Janky-Jingle-Crew/NorthPoleCircuit/Media/decorations.jpg

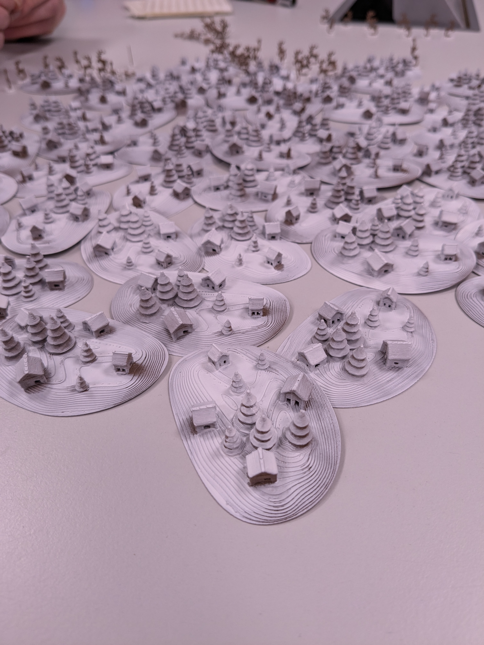
Media/decorations.jpg
