Janky-Jingle-Crew/NorthPoleCircuit/Media/decorations_2.jpg

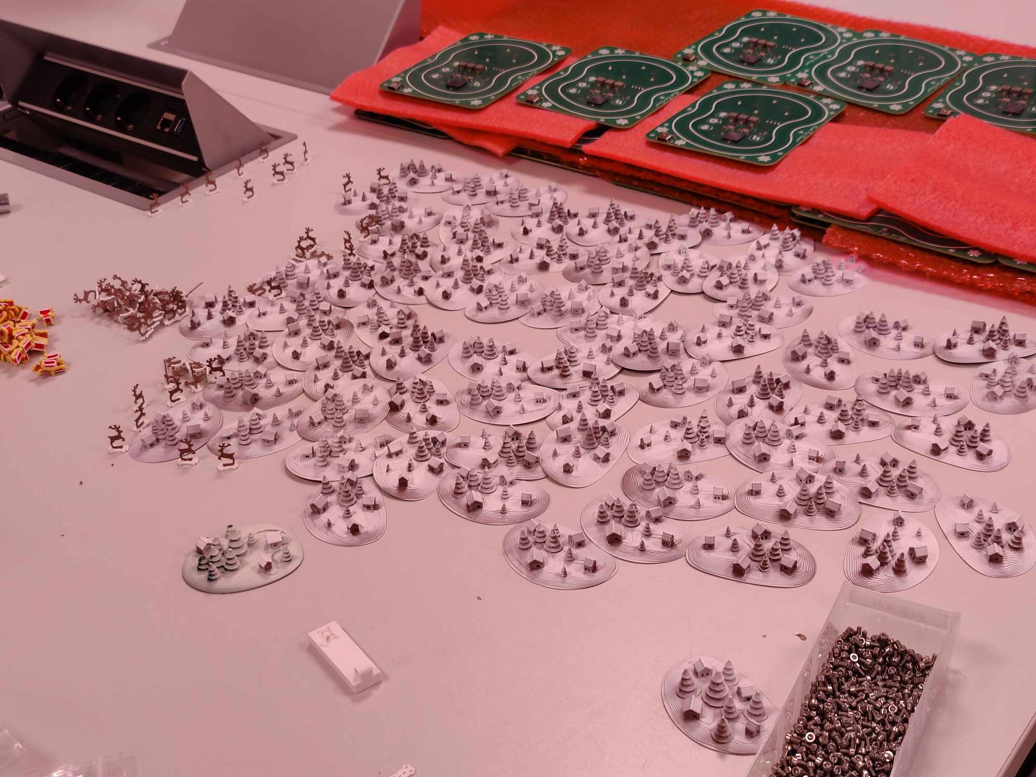
Media/decorations_2.jpg
