Janky-Jingle-Crew/NorthPoleCircuit/Media/decorations_3.jpg

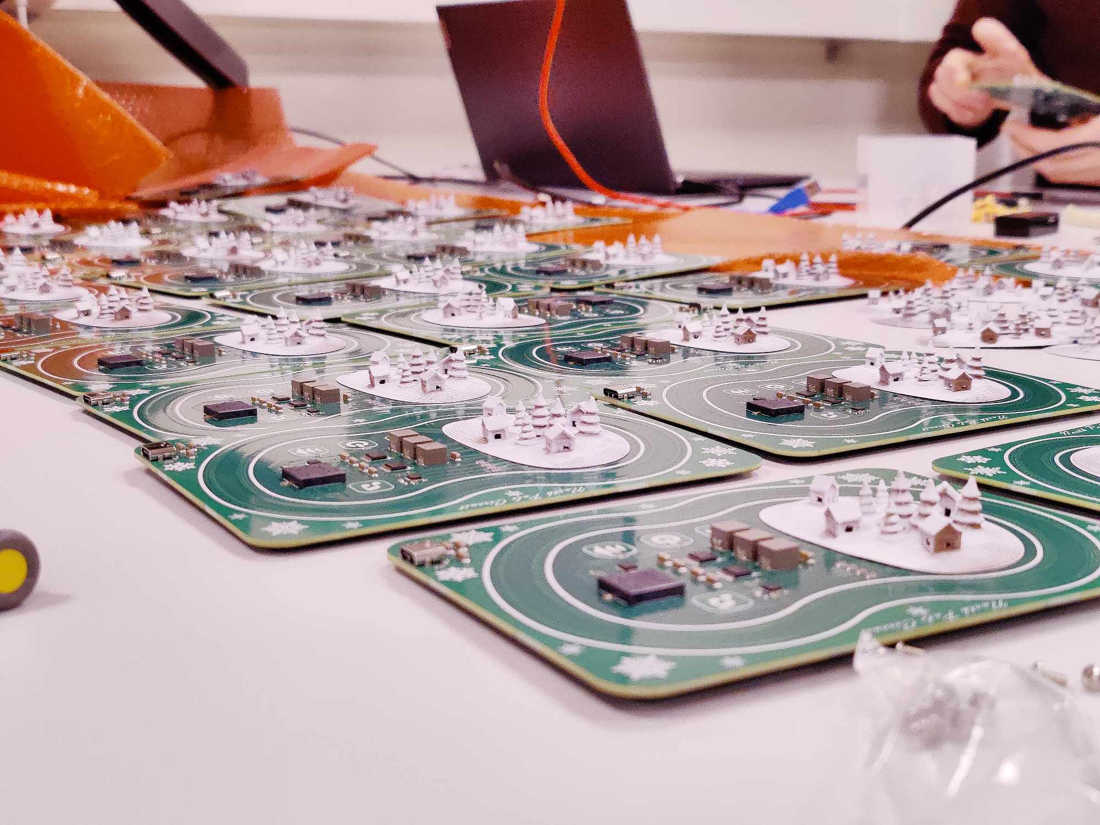
Media/decorations_3.jpg
