Janky-Jingle-Crew/NorthPoleCircuit/Media/pcbs.jpg

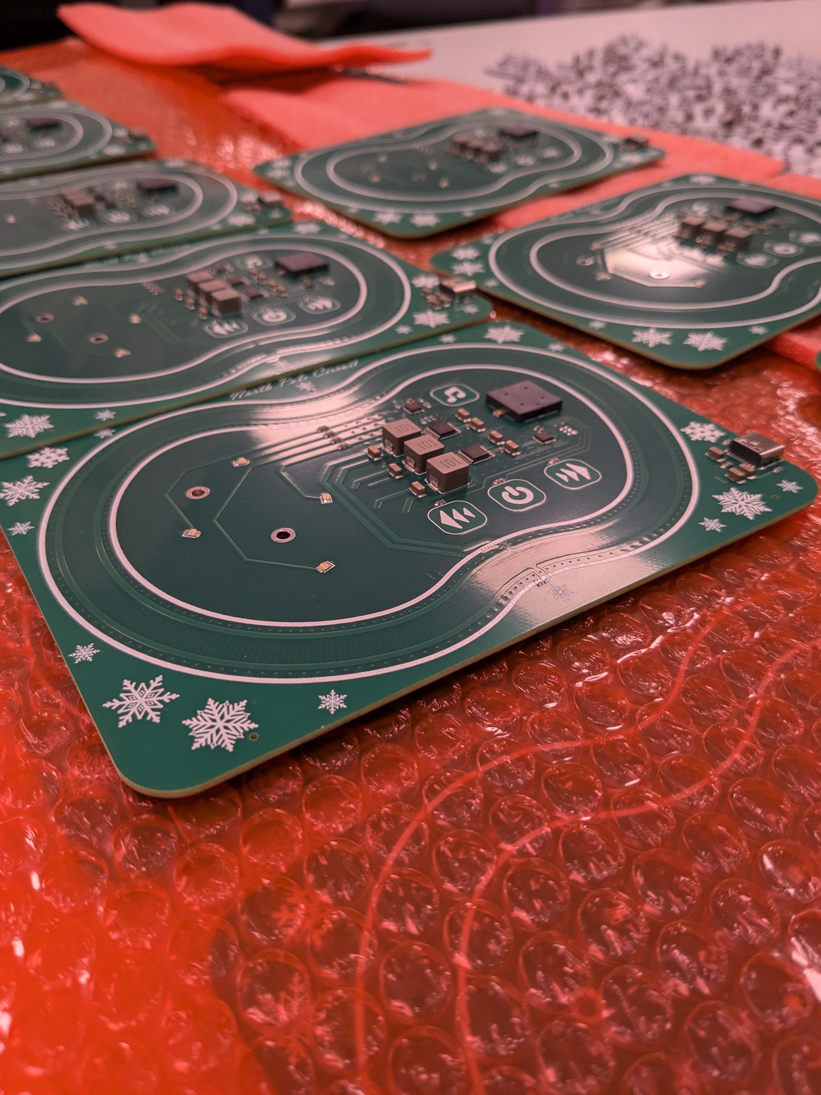
Media/pcbs.jpg
