Janky-Jingle-Crew/NorthPoleCircuit/Media/production_glueing.jpg

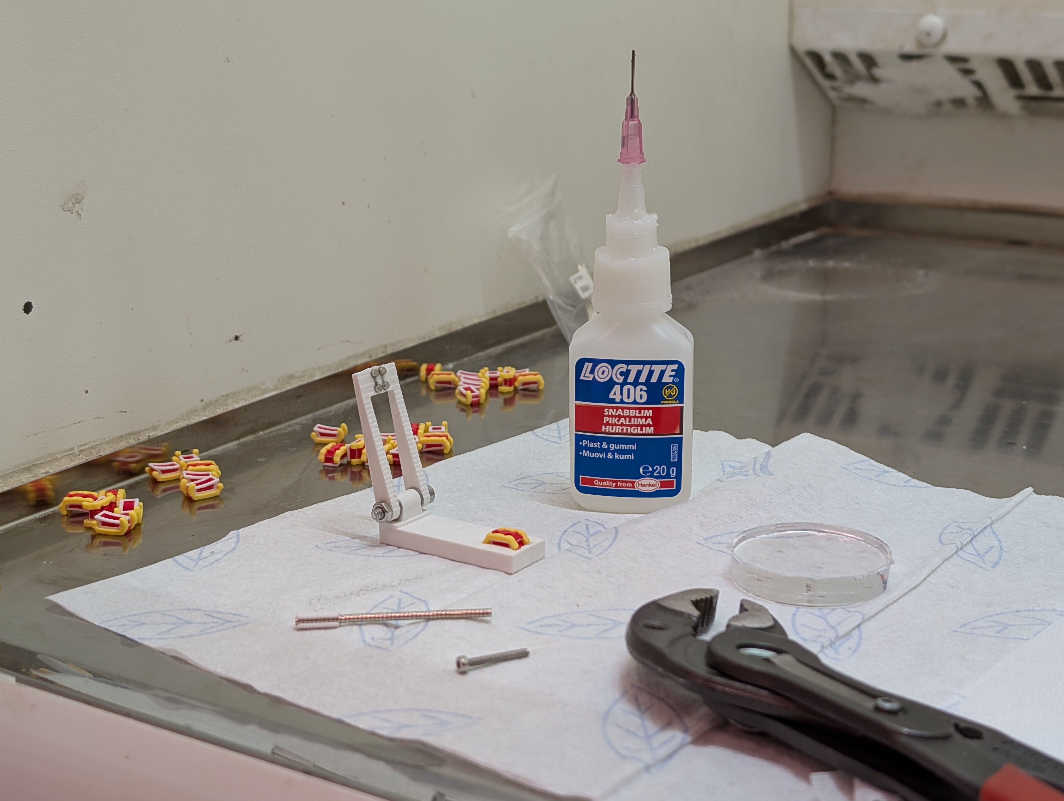
Media/production_glueing.jpg
