Janky-Jingle-Crew/NorthPoleCircuit/Media/single_decoration_2.jpg

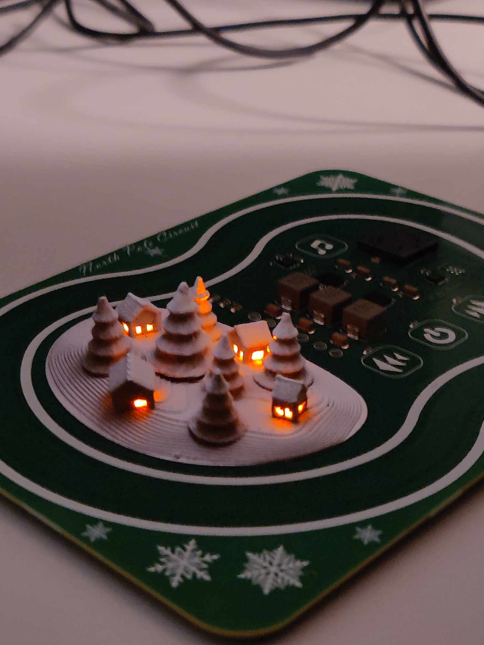
Media/single_decoration_2.jpg
