Janky-Jingle-Crew/NorthPoleCircuit/PCB/Pictures/Edwardian Script ITC 350/text_and_a_happy_new_year.png

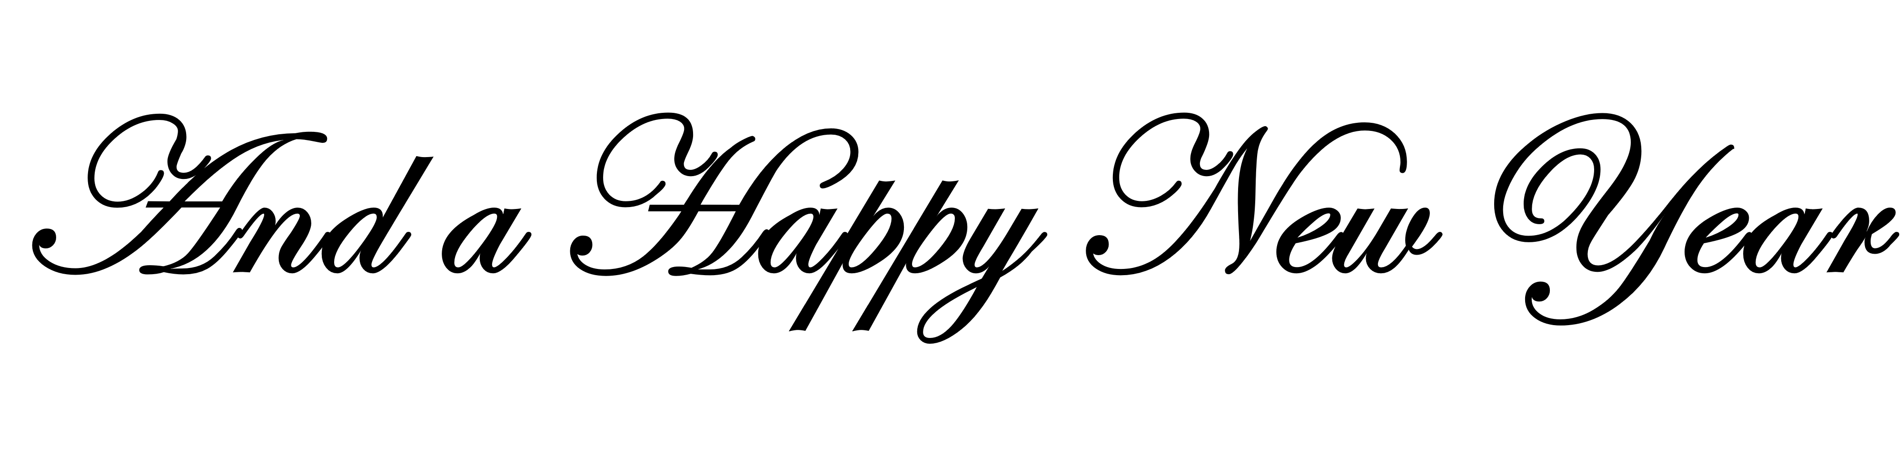
PCB/Pictures/Edwardian Script ITC 350/text_and_a_happy_new_year.png
