Janky-Jingle-Crew/NorthPoleCircuit/PCB/Pictures/Edwardian Script ITC 350/text_DQ.png

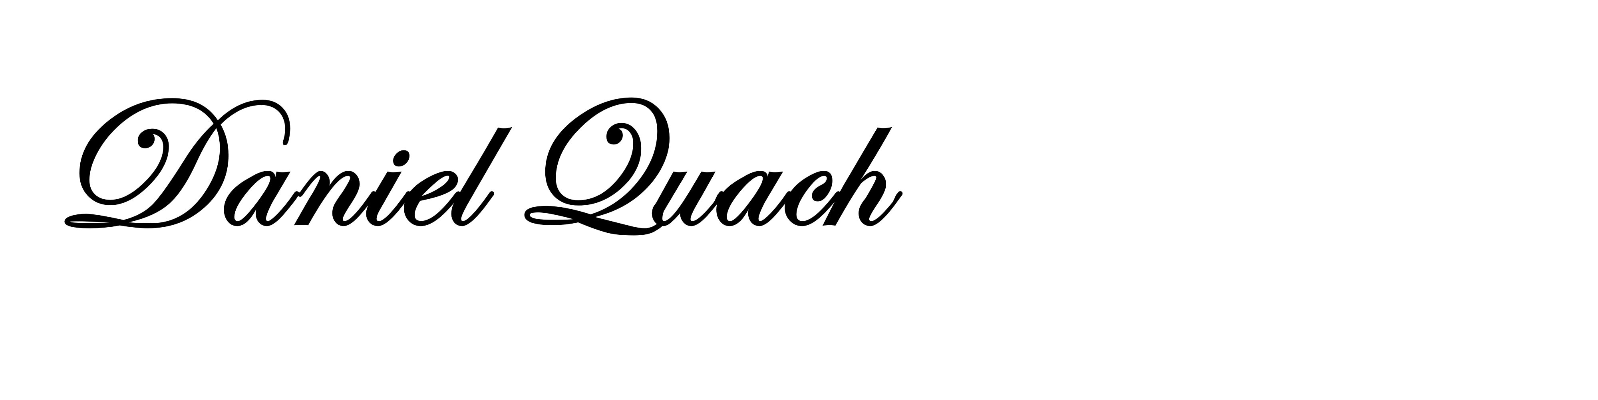
PCB/Pictures/Edwardian Script ITC 350/text_DQ.png
