Janky-Jingle-Crew/NorthPoleCircuit/PCB/Pictures/Edwardian Script ITC 350/text_GA.png

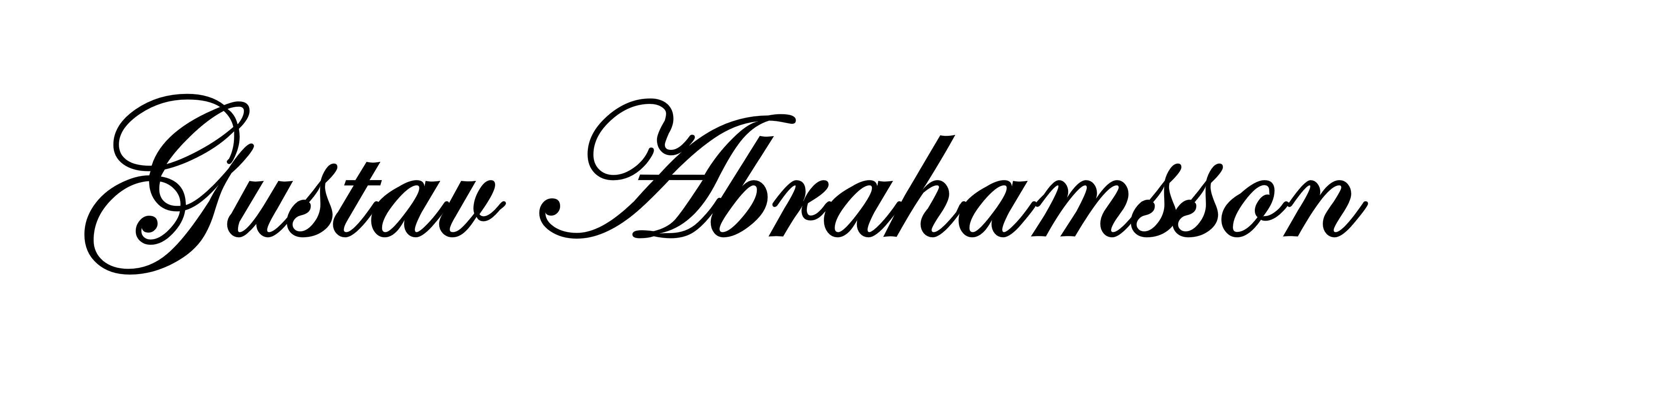
PCB/Pictures/Edwardian Script ITC 350/text_GA.png
