Janky-Jingle-Crew/NorthPoleCircuit/PCB/Pictures/Edwardian Script ITC 350/text_janky_jingle_crew_2024.png

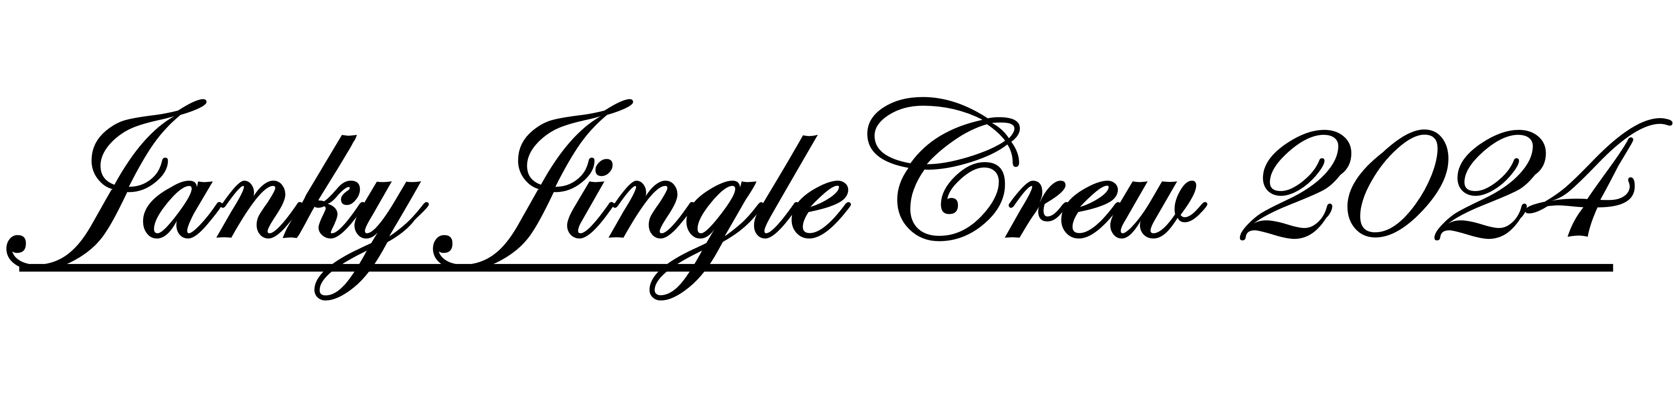
PCB/Pictures/Edwardian Script ITC 350/text_janky_jingle_crew_2024.png
