Janky-Jingle-Crew/NorthPoleCircuit/PCB/Pictures/Edwardian Script ITC 350/text_JW.png

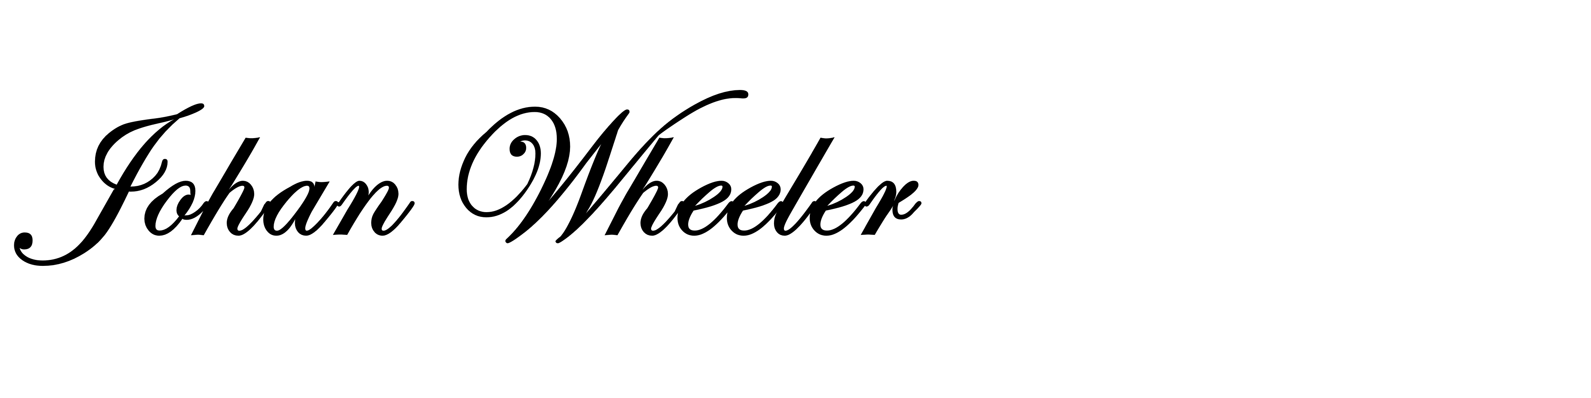
PCB/Pictures/Edwardian Script ITC 350/text_JW.png
