Janky-Jingle-Crew/NorthPoleCircuit/PCB/Pictures/Edwardian Script ITC 350/text_merry_christmas.png

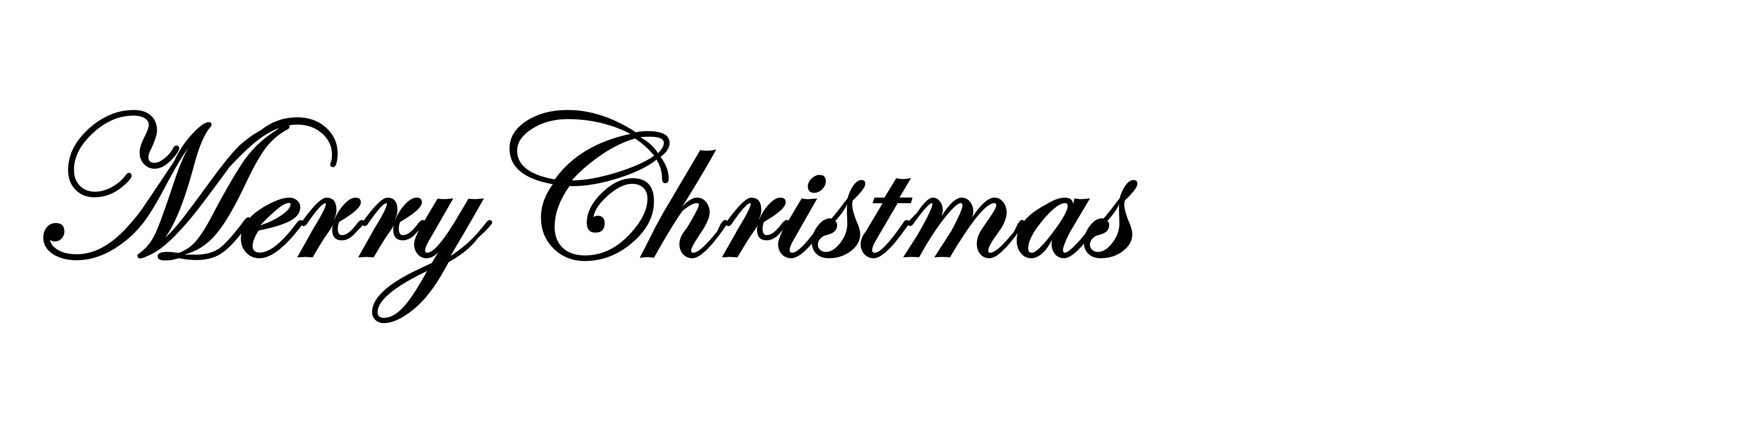
PCB/Pictures/Edwardian Script ITC 350/text_merry_christmas.png
