Janky-Jingle-Crew/NorthPoleCircuit/PCB/Pictures/Edwardian Script ITC 350/text_north_pole_circuit.png

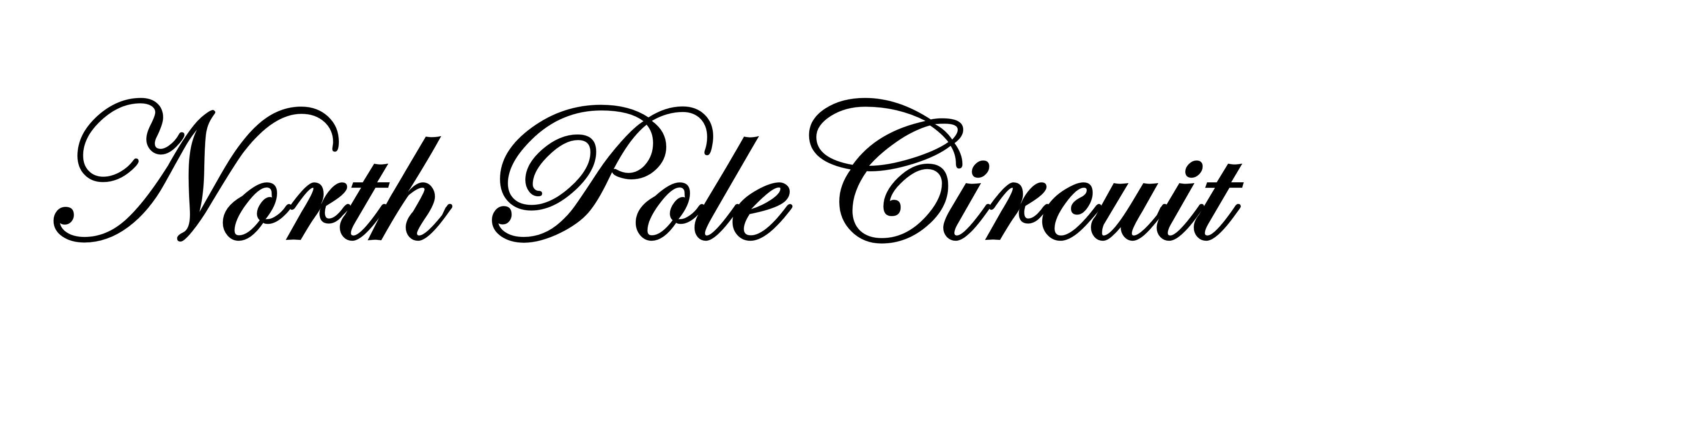
PCB/Pictures/Edwardian Script ITC 350/text_north_pole_circuit.png
