Janky-Jingle-Crew/NorthPoleCircuit/PCB/Pictures/Kunsler Script 350/text_AA.png

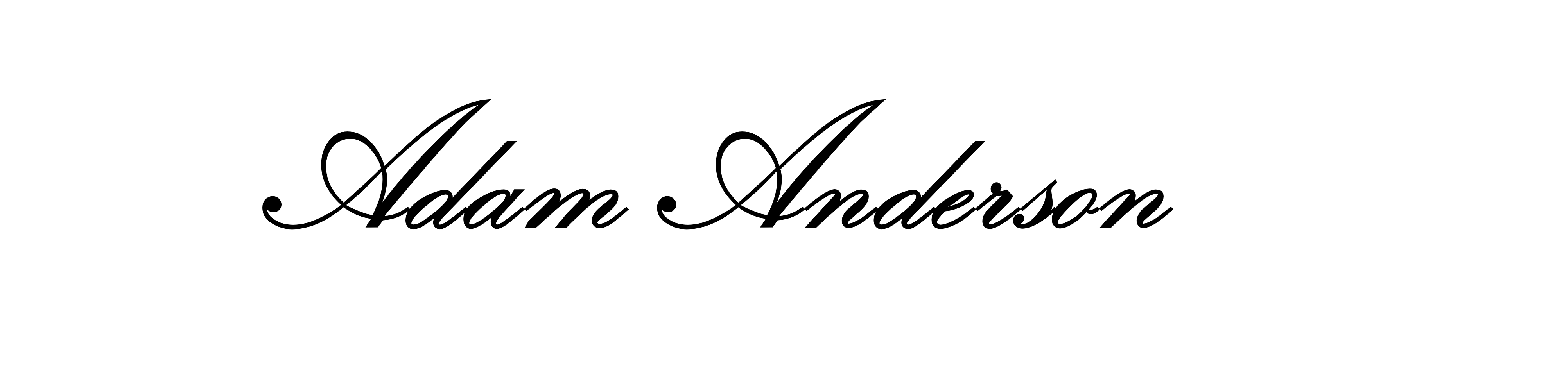
PCB/Pictures/Kunsler Script 350/text_AA.png
