Janky-Jingle-Crew/NorthPoleCircuit/PCB/Pictures/Kunsler Script 350/text_and_a_happy_new_year_small_a.png

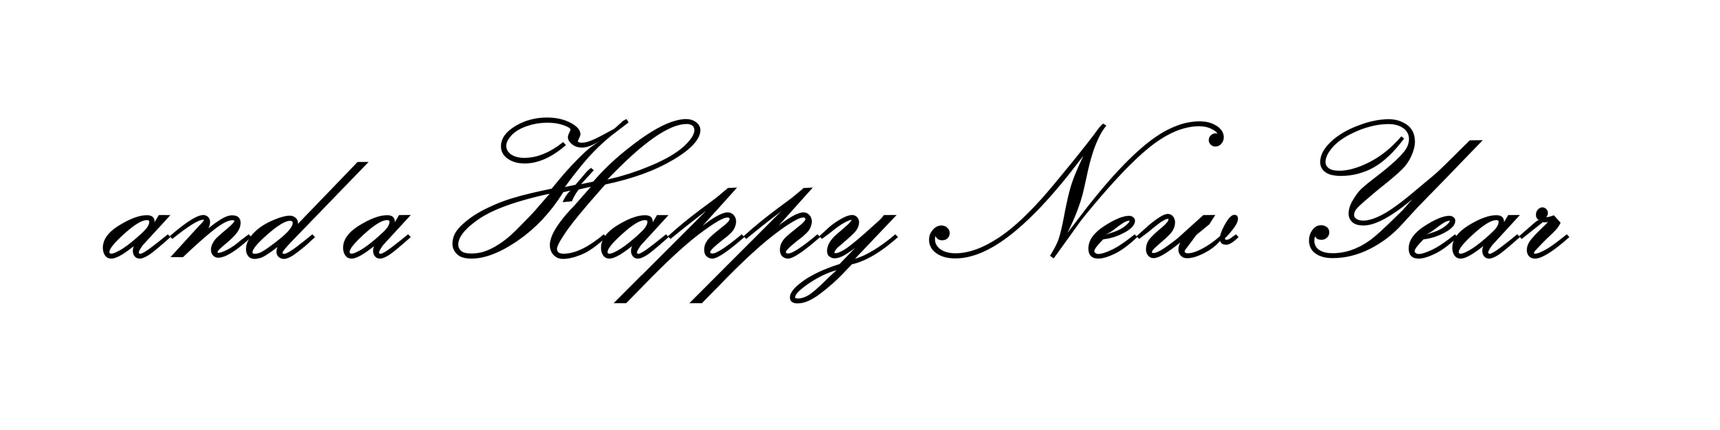
PCB/Pictures/Kunsler Script 350/text_and_a_happy_new_year_small_a.png
