Janky-Jingle-Crew/NorthPoleCircuit/PCB/Pictures/Kunsler Script 350/text_DQ.png

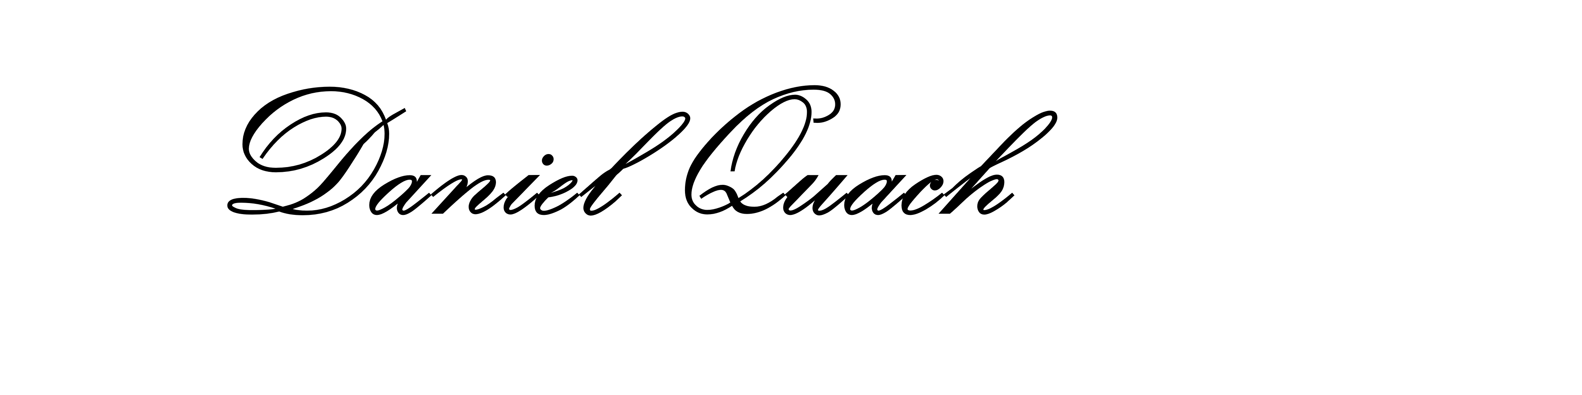
PCB/Pictures/Kunsler Script 350/text_DQ.png
