Janky-Jingle-Crew/NorthPoleCircuit/PCB/Pictures/Kunsler Script 350/text_GA.png

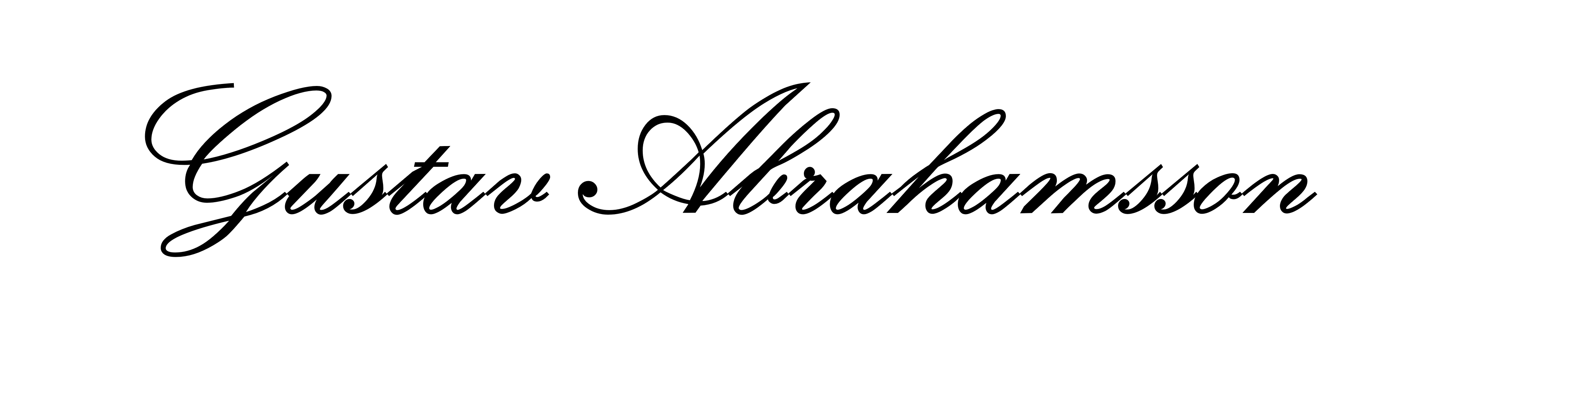
PCB/Pictures/Kunsler Script 350/text_GA.png
