Janky-Jingle-Crew/NorthPoleCircuit/PCB/Pictures/Kunsler Script 350/text_jankyjinglecrew.png

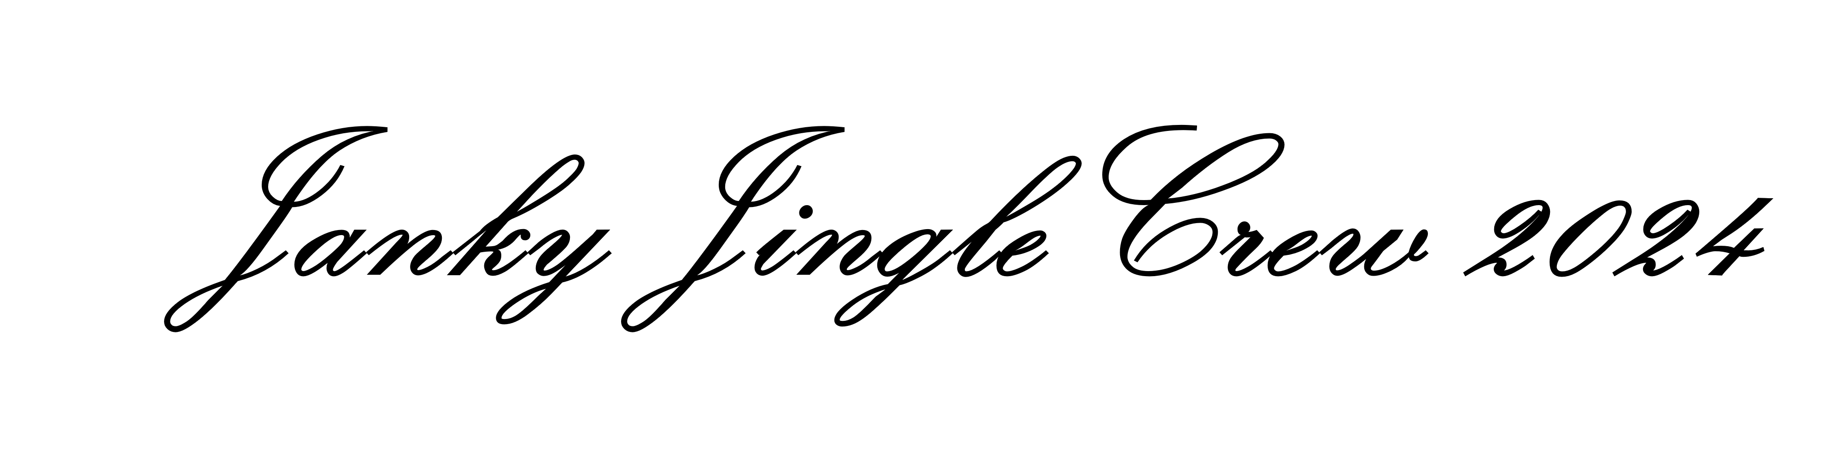
PCB/Pictures/Kunsler Script 350/text_jankyjinglecrew.png
