Janky-Jingle-Crew/NorthPoleCircuit/PCB/Pictures/Kunsler Script 350/text_northpolecircuit.png

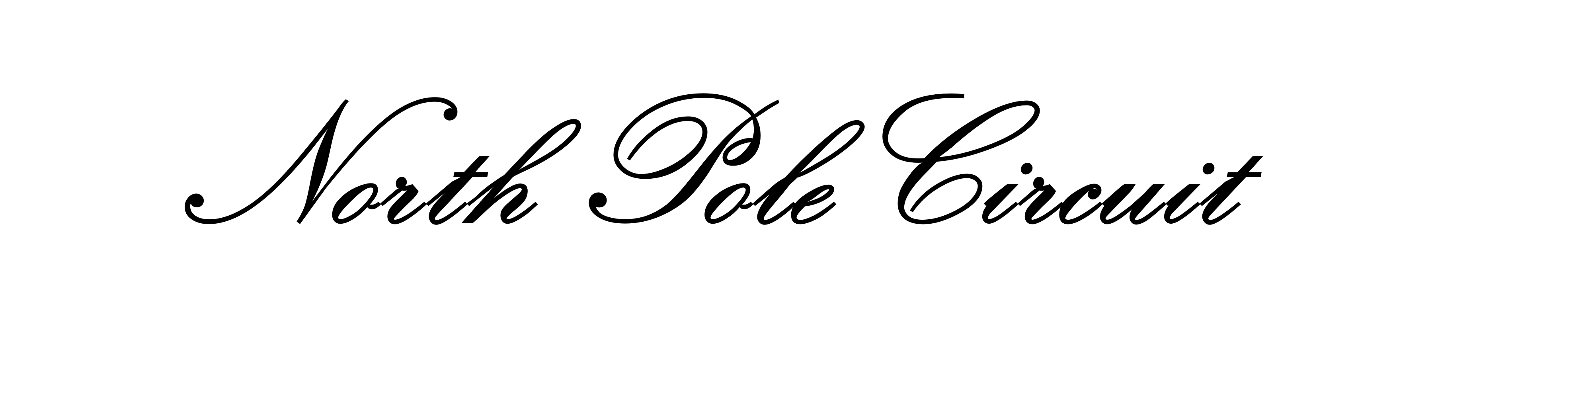
PCB/Pictures/Kunsler Script 350/text_northpolecircuit.png
