Janky-Jingle-Crew/NorthPoleCircuit/PCB/Pictures/Kunsler Script 350/text_och_gott_nytt_ar.png

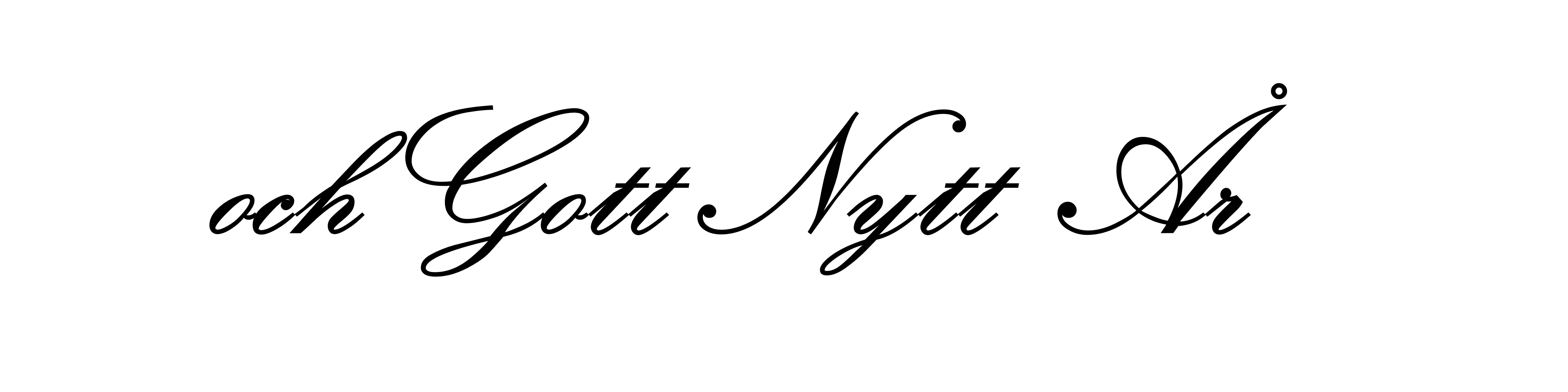
PCB/Pictures/Kunsler Script 350/text_och_gott_nytt_ar.png
