Janky-Jingle-Crew/NorthPoleCircuit/PCB/Pictures/snowflake1.png

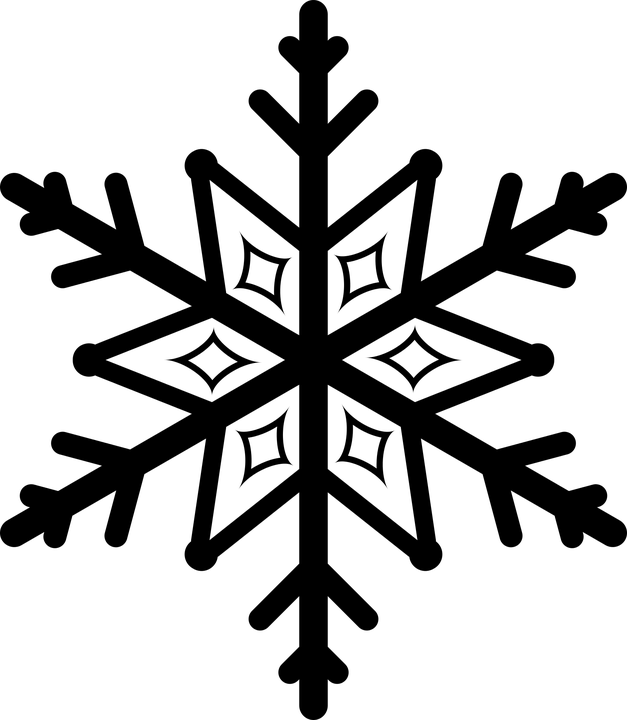
PCB/Pictures/snowflake1.png
