Janky-Jingle-Crew/NorthPoleCircuit/PCB/Pictures/snowflake2.png

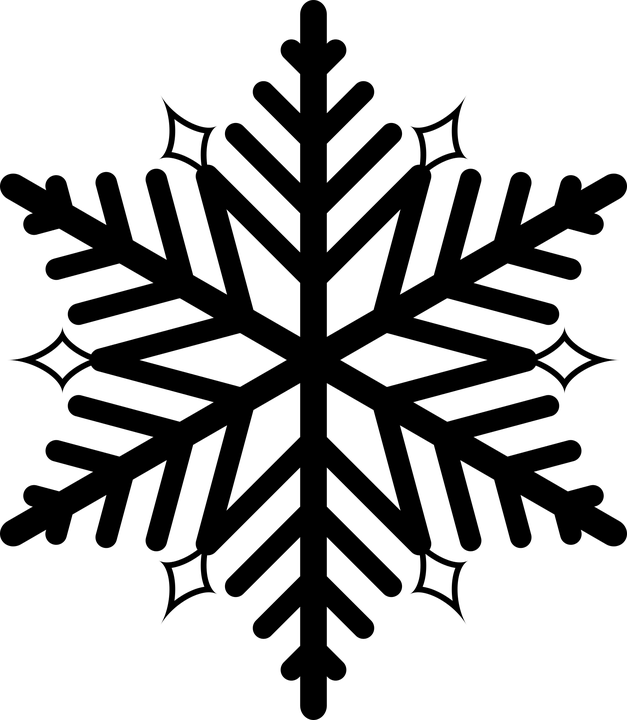
PCB/Pictures/snowflake2.png
