Janky-Jingle-Crew/NorthPoleCircuit/PCB/Pictures/snowflake3.png

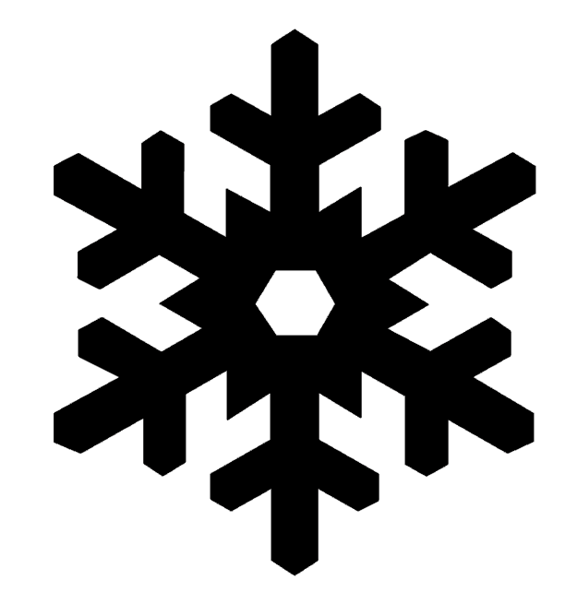
PCB/Pictures/snowflake3.png
