Janky-Jingle-Crew/NorthPoleCircuit/PCB/Pictures/text.png

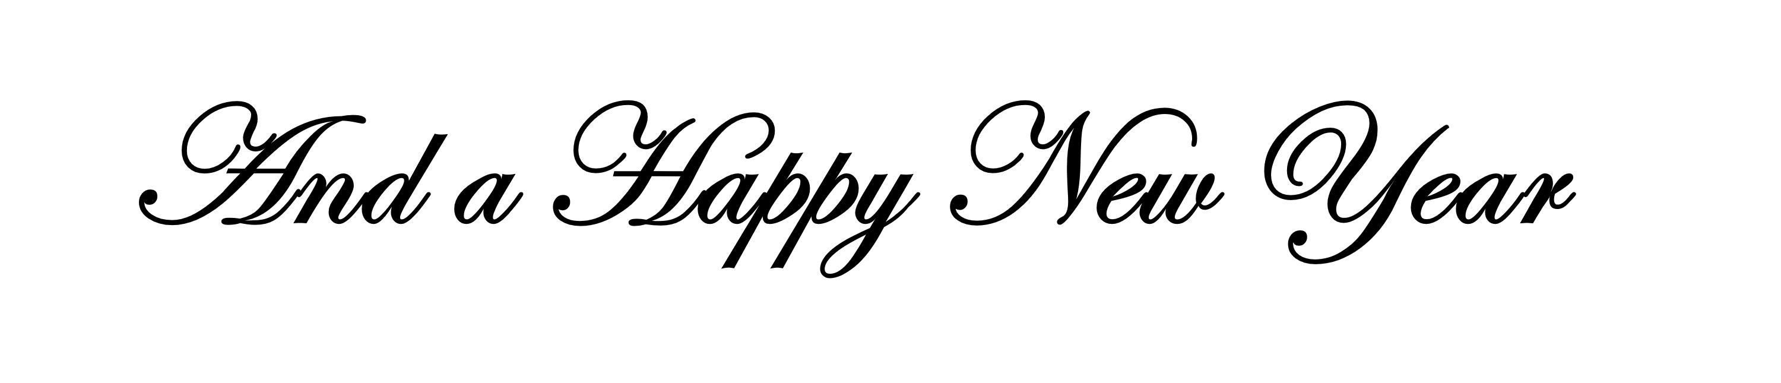
PCB/Pictures/text.png
