Janky-Jingle-Crew/NorthPoleCircuit/PCB/Pictures/Vladimir Script 350/AA.png

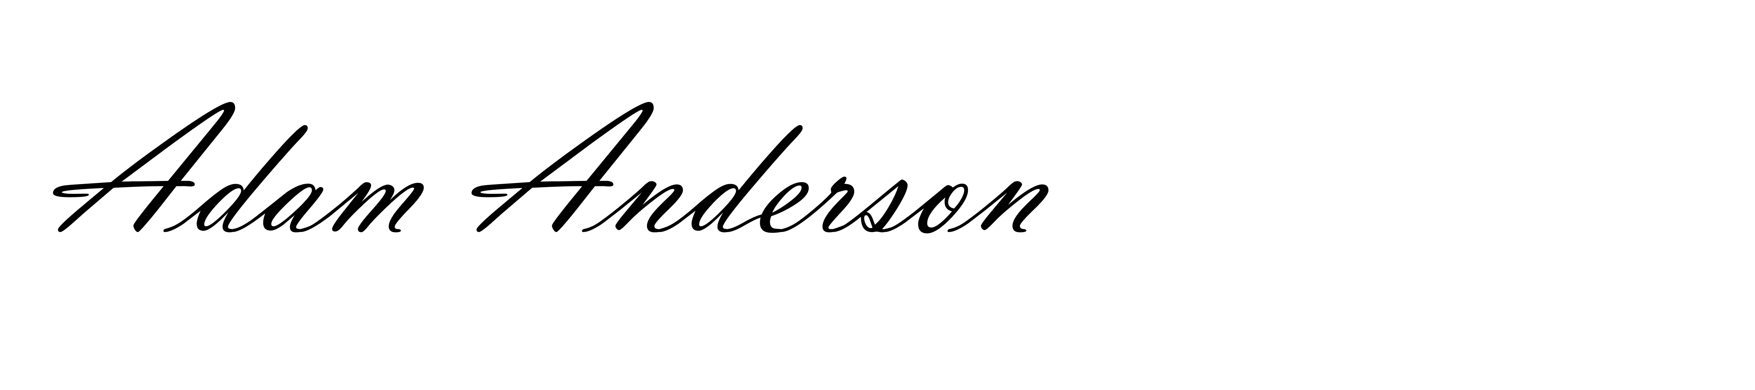
PCB/Pictures/Vladimir Script 350/AA.png
