Janky-Jingle-Crew/NorthPoleCircuit/PCB/Pictures/Vladimir Script 350/and a happy new year.png

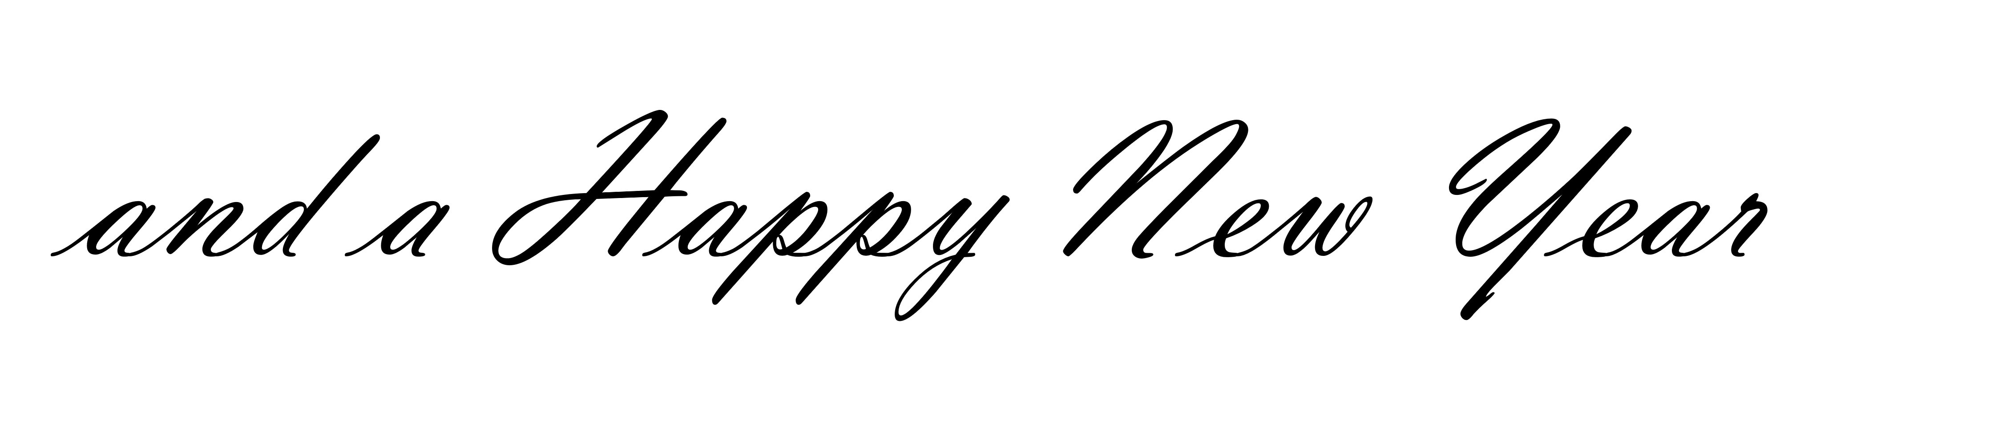
PCB/Pictures/Vladimir Script 350/and a happy new year.png
