Janky-Jingle-Crew/NorthPoleCircuit/PCB/Pictures/Vladimir Script 350/DQ.png

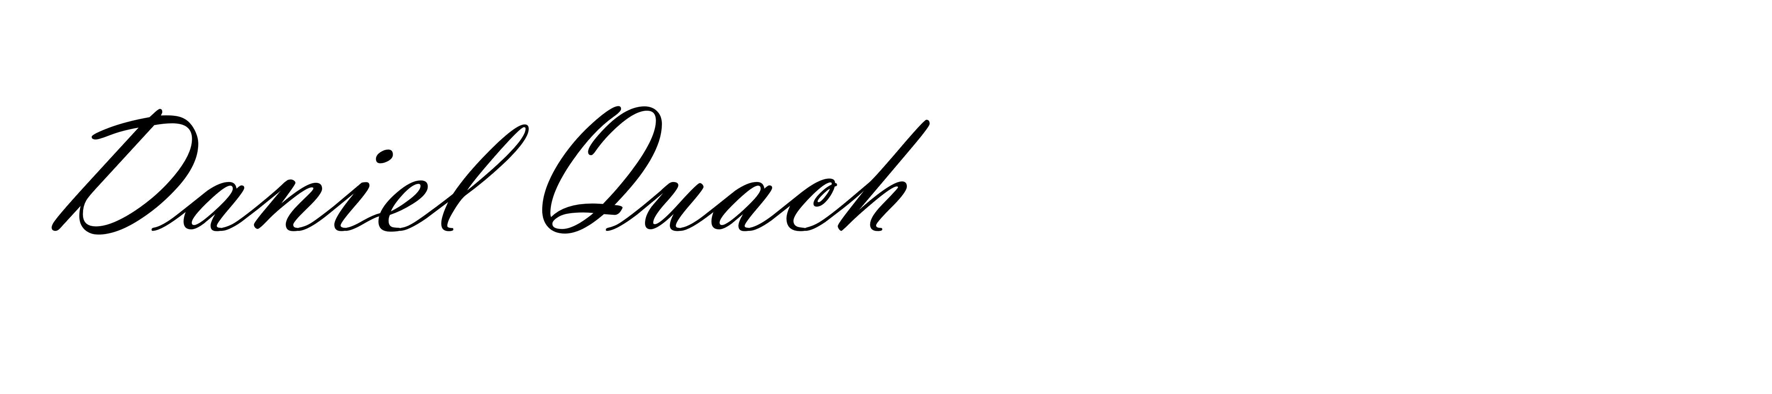
PCB/Pictures/Vladimir Script 350/DQ.png
