Janky-Jingle-Crew/NorthPoleCircuit/PCB/Pictures/Vladimir Script 350/GA.png

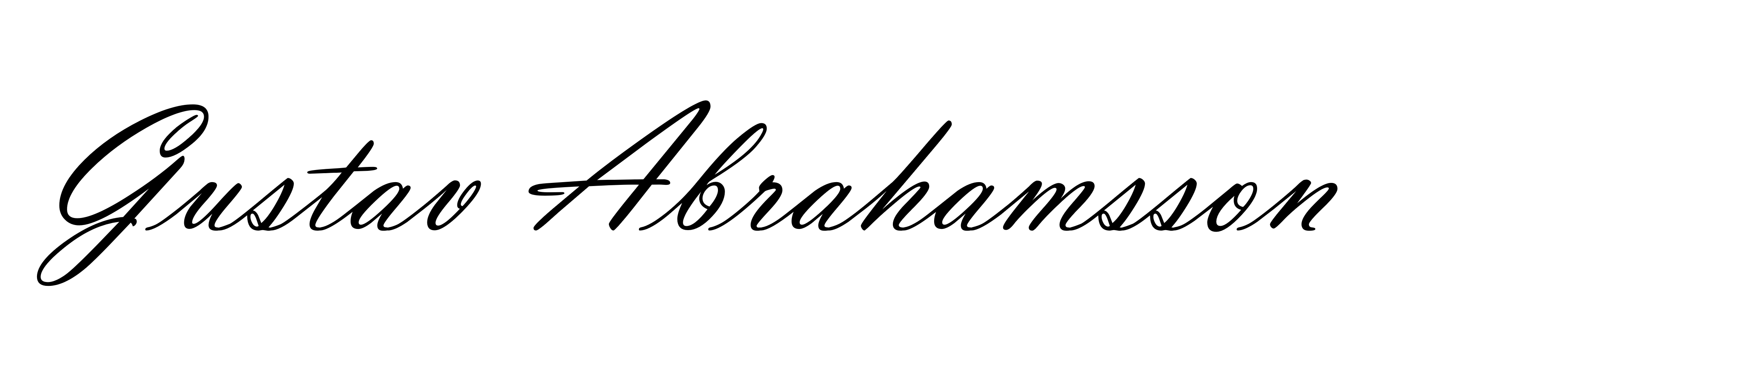
PCB/Pictures/Vladimir Script 350/GA.png
