Janky-Jingle-Crew/NorthPoleCircuit/PCB/Pictures/Vladimir Script 350/janky jingle crew.png

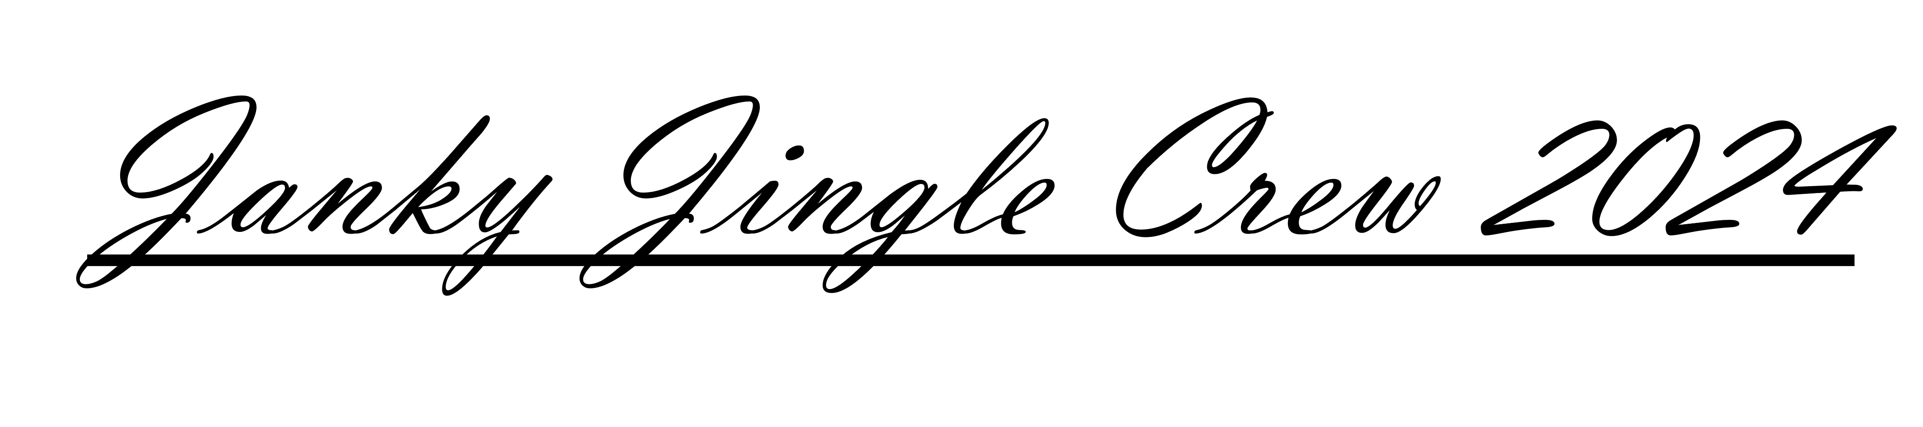
PCB/Pictures/Vladimir Script 350/janky jingle crew.png
