Janky-Jingle-Crew/NorthPoleCircuit/PCB/Pictures/Vladimir Script 350/north pole circuit.png

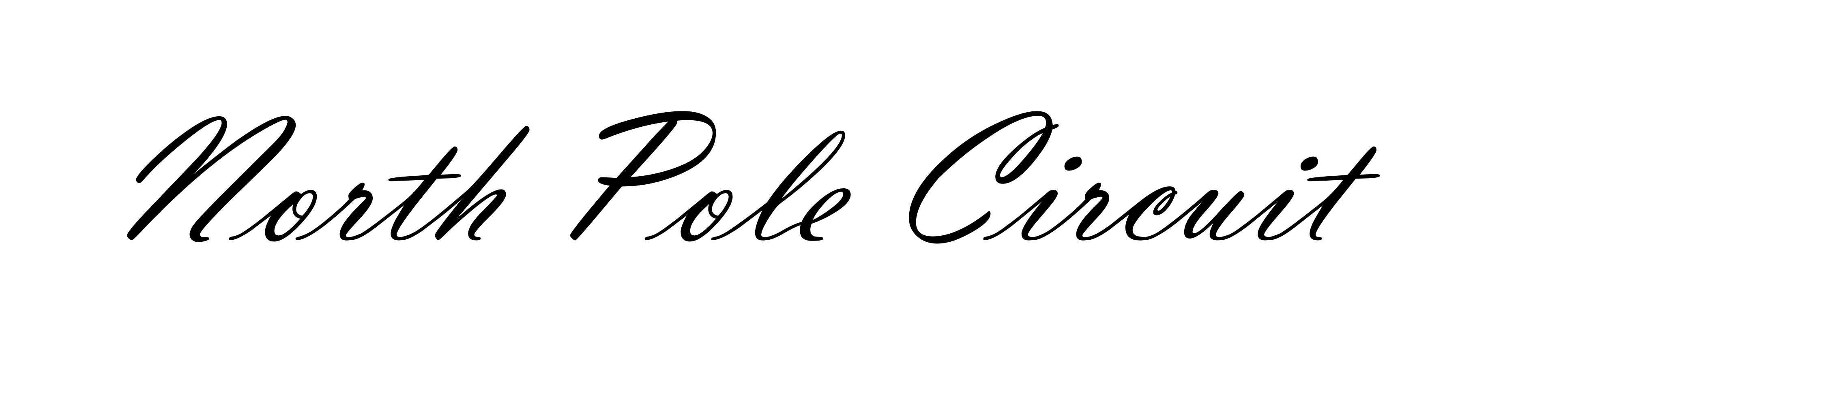
PCB/Pictures/Vladimir Script 350/north pole circuit.png
