Janky-Jingle-Crew/NorthPoleCircuit/PCB/Pictures/Vladimir Script 350/santa sillouette.png

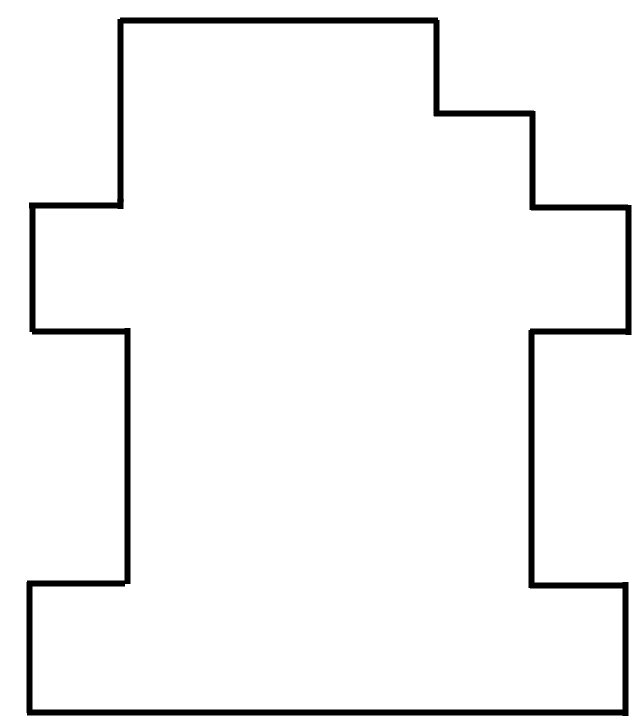
PCB/Pictures/Vladimir Script 350/santa sillouette.png
