Janky-Jingle-Crew/NorthPoleCircuit/PCB/Pictures/Vladimir Script 350/text_och_gott_nytt_ar.png

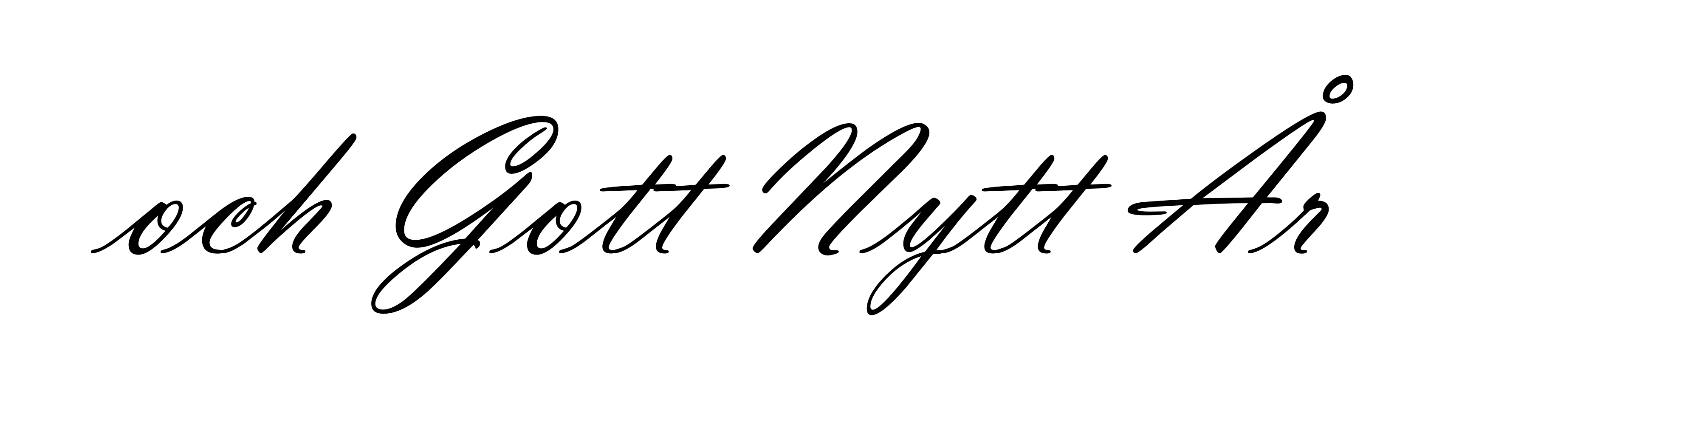
PCB/Pictures/Vladimir Script 350/text_och_gott_nytt_ar.png
