Janky-Jingle-Crew/NorthPoleCircuit/PCB/NorthPoleCircuit_PCB.kicad_sch

## KiCad design PCB/NorthPoleCircuit_PCB.kicad_sch (2024-11-26)

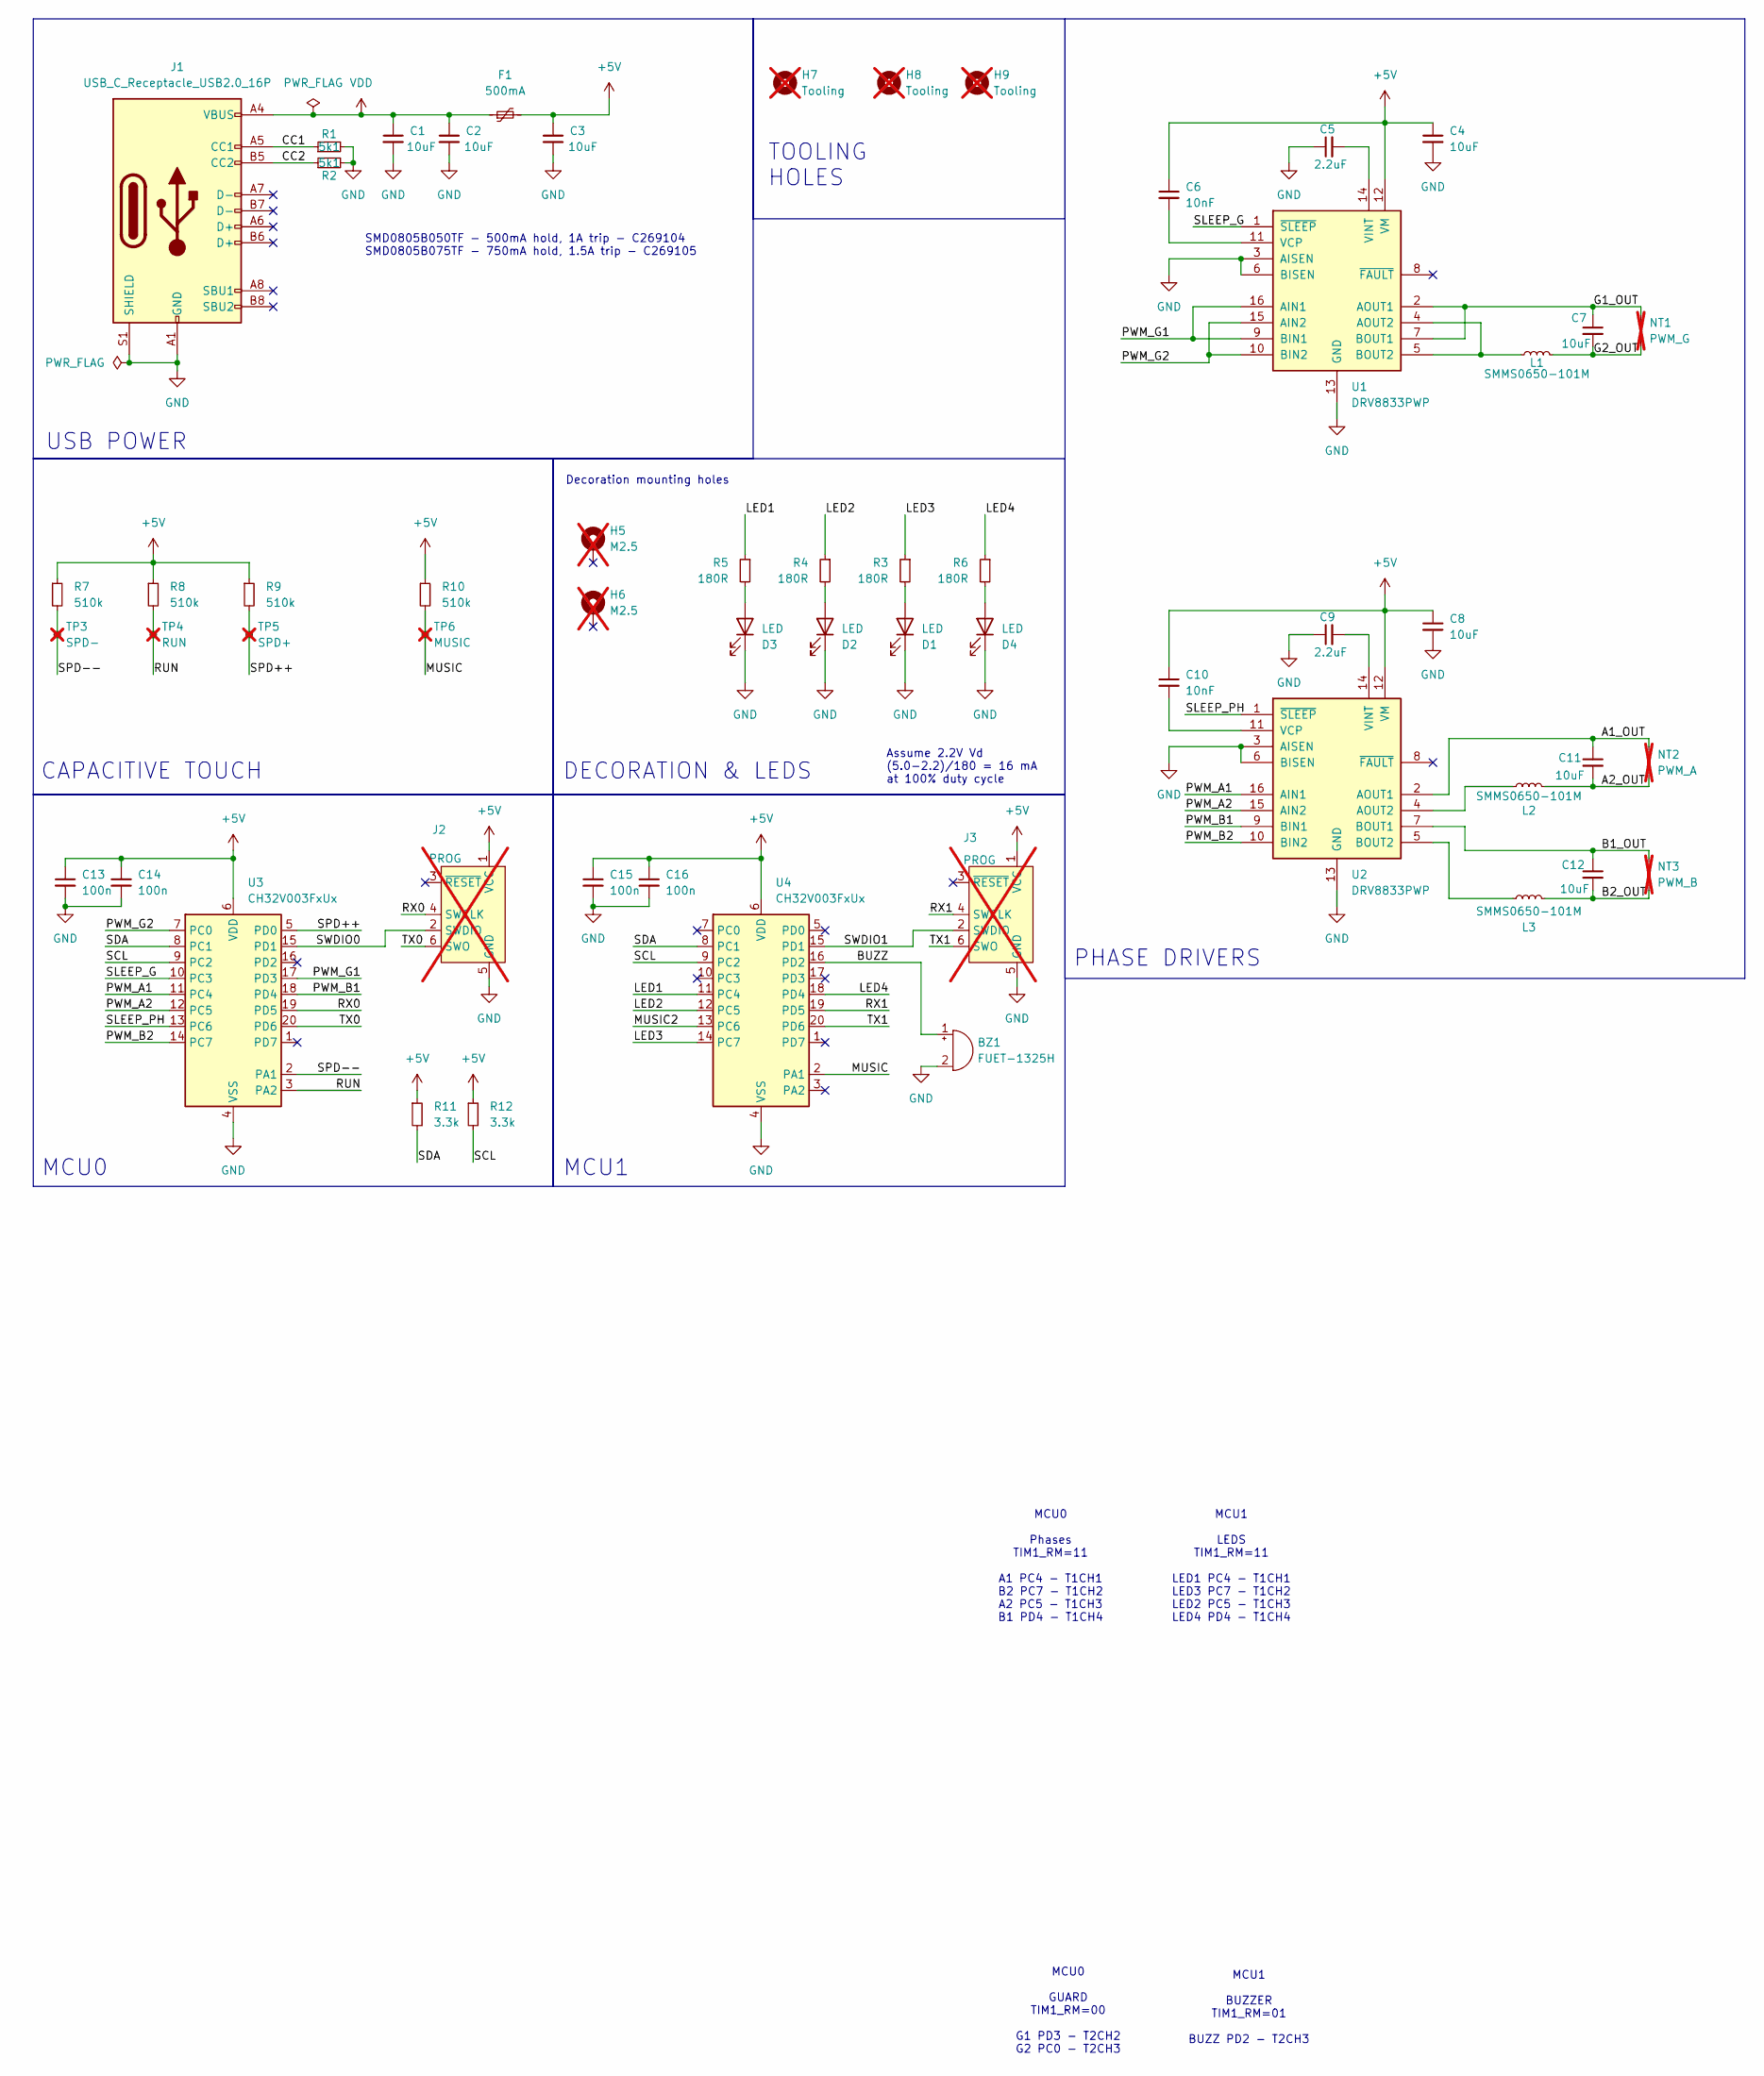
[picture p55: schematic NorthPoleCircuit_PCB.kicad_sch]

Parts:
BZ1: FUET-1325H; FUET-1325; MPN C2982583
C1, C2, C3, C4, C7, C8, C11, C12: 10uF; C_1206_3216Metric; MPN C13585
C5, C9: 2.2uF; C_1206_3216Metric; MPN C50254
C6, C10: 10nF; C_0402_1005Metric; MPN C15195
C13, C14, C15, C16: 100n; C_0402_1005Metric; MPN C1525
D1, D2, D3, D4: LED; LED_0805_2012Metric; MPN C5878906
F1: 500mA; Fuse_0805_2012Metric; MPN C269104
H5, H6: M2.5; MountingHole_2.7mm_M2.5_DIN965_Pad; not fitted
H7, H8, H9: Tooling; tooling_hole; not fitted
J1: USB_C_Receptacle_USB2.0_16P; USB_C_Receptacle_HRO_TYPE-C-31-M-12; MPN C165948
J2, J3: PROG; Tag-Connect_TC2030-IDC-NL_2x03_P1.27mm_Vertical; not fitted
L1, L2, L3: SMMS0650-101M; MPN C2894722
NT1: PWM_G; NetTie_1.25mm; not fitted
NT2: PWM_A; NetTie_1.25mm; not fitted
NT3: PWM_B; NetTie_1.25mm; not fitted
R1, R2: 5k1; R_0603_1608Metric; MPN C23186
R3, R4, R5, R6: 180R; R_0805_2012Metric; MPN C25270
R7, R8, R9, R10: 510k; R_0603_1608Metric; MPN C23192
R11, R12: 3.3k; R_0402_1005Metric; MPN C25890
TP3: SPD-; Cap_Touch_10mm; not fitted
TP4: RUN; Cap_Touch_10mm; not fitted
TP5: SPD+; Cap_Touch_10mm; not fitted
TP6: MUSIC; Cap_Touch_10mm; not fitted
U1, U2: DRV8833PWP; HTSSOP-16-1EP_4.4x5mm_P0.65mm_EP3.4x5mm_Mask2.46x2.31mm_The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; MPN C50506
U3, U4: CH32V003FxUx; QFN-20-1EP_3x3mm_P0.4mm_EP1.65x1.65mm; MPN C5299908

Connections:
+5V: C3.1, C4.1, C6.1, C8.1, C10.1, C13.1, C14.1, C15.1, C16.1, F1.2, J2.1 (VCC), J3.1 (VCC), R7.1, R8.1, R9.1, R10.1, R11.1, R12.1, U1.12 (VM), U2.12 (VM), U3.6 (VDD), U4.6 (VDD)
A1_OUT: C11.1, NT2.2, U2.2 (AOUT1)
A2_OUT: C11.2, L2.2, NT2.1
B1_OUT: C12.1, NT3.2, U2.7 (BOUT1)
B2_OUT: C12.2, L3.2, NT3.1
BUZZ: BZ1.1 (+), U4.16 (PD2)
CC1: J1.A5 (CC1), R1.1
CC2: J1.B5 (CC2), R2.1
G1_OUT: C7.1, NT1.2, U1.2 (AOUT1), U1.7 (BOUT1)
G2_OUT: C7.2, L1.2, NT1.1
GND: BZ1.2 (-), C1.2, C2.2, C3.2, C4.2, C5.1, C8.2, C9.1, C13.2, C14.2, C15.2, C16.2, D1.1 (K), D2.1 (K), D3.1 (K), D4.1 (K), J1.A1 (GND), J1.A12 (GND), J1.B1 (GND), J1.B12 (GND), J1.S1 (SHIELD), J2.5 (GND), J3.5 (GND), R1.2, R2.2, U1.3 (AISEN), U1.6 (BISEN), U1.13 (GND), U1.17 (GND), U2.3 (AISEN), U2.6 (BISEN), U2.13 (GND), U2.17 (GND), U3.4 (VSS), U3.21 (VSS), U4.4 (VSS), U4.21 (VSS)
LED1: R5.1, U4.11 (PC4)
LED2: R4.1, U4.12 (PC5)
LED3: R3.1, U4.14 (PC7)
LED4: R6.1, U4.18 (PD4)
MUSIC: R10.2, TP6.1, U4.2 (PA1)
MUSIC2: U4.13 (PC6)
unnamed: C5.2, U1.14 (VINT)
unnamed: C6.2, U1.11 (VCP)
unnamed: C9.2, U2.14 (VINT)
unnamed: C10.2, U2.11 (VCP)
unnamed: D1.2 (A), R3.2
unnamed: D2.2 (A), R4.2
unnamed: D3.2 (A), R5.2
unnamed: D4.2 (A), R6.2
unnamed: L1.1, U1.4 (AOUT2), U1.5 (BOUT2)
unnamed: L2.1, U2.4 (AOUT2)
unnamed: L3.1, U2.5 (BOUT2)
PWM_A1: U2.16 (AIN1), U3.11 (PC4)
PWM_A2: U2.15 (AIN2), U3.12 (PC5)
PWM_B1: U2.9 (BIN1), U3.18 (PD4)
PWM_B2: U2.10 (BIN2), U3.14 (PC7)
PWM_G1: U1.9 (BIN1), U1.16 (AIN1), U3.17 (PD3)
PWM_G2: U1.10 (BIN2), U1.15 (AIN2), U3.7 (PC0)
RUN: R8.2, TP4.1, U3.3 (PA2)
RX0: J2.4 (SWCLK), U3.19 (PD5)
RX1: J3.4 (SWCLK), U4.19 (PD5)
SCL: R12.2, U3.9 (PC2), U4.9 (PC2)
SDA: R11.2, U3.8 (PC1), U4.8 (PC1)
SLEEP_G: U1.1 (~SLEEP), U3.10 (PC3)
SLEEP_PH: U2.1 (~SLEEP), U3.13 (PC6)
SPD++: R9.2, TP5.1, U3.5 (PD0)
SPD--: R7.2, TP3.1, U3.2 (PA1)
SWDIO0: J2.2 (SWDIO), U3.15 (PD1)
SWDIO1: J3.2 (SWDIO), U4.15 (PD1)
TX0: J2.6 (SWO), U3.20 (PD6)
TX1: J3.6 (SWO), U4.20 (PD6)
VDD: C1.1, C2.1, F1.1, J1.A4 (VBUS), J1.A9 (VBUS), J1.B4 (VBUS), J1.B9 (VBUS)

Notes on the sheet:
MCU0
DECORATION & LEDS
USB POWER
SMD0805B050TF - 500mA hold, 1A trip - C269104 SMD0805B075TF - 750mA hold, 1.5A trip - C269105
CAPACITIVE TOUCH
MCU1 BUZZER TIM1_RM=01 BUZZ PD2 - T2CH3
MCU0 GUARD TIM1_RM=00 G1 PD3 - T2CH2 G2 PC0 - T2CH3
MCU0 Phases TIM1_RM=11 A1 PC4 - T1CH1 B2 PC7 - T1CH2 A2 PC5 - T1CH3 B1 PD4 - T1CH4
Decoration mounting holes
TOOLING HOLES
MCU1
Assume 2.2V Vd (5.0-2.2)/180 = 16 mA at 100% duty cycle
PHASE DRIVERS
MCU1 LEDS TIM1_RM=11 LED1 PC4 - T1CH1 LED3 PC7 - T1CH2 LED2 PC5 - T1CH3 LED4 PD4 - T1CH4
