Janky-Jingle-Crew/NorthPoleCircuit/Code/Decoration_Control/src/funconfig.h

#ifndef FUNCONFIG_H_
#define FUNCONFIG_H_

#define CH32V003 1

#define FUNCONF_SYSTICK_USE_HCLK 1
#define FUNCONF_USE_DEBUGPRINTF 0
#define FUNCONF_USE_UARTPRINTF 1
#define FUNCONF_UART_PRINTF_BAUD 115200

// Project specific defines


#endif
